ISLRfid/hitag2-emulator/hardware/kicad/HiTag2_Emulator.kicad_sch

## KiCad design hardware/kicad/HiTag2_Emulator.kicad_sch (2025-12-26)

Schematic: HiTag2_Emulator.kicad_sch

Parts:
C1: 22µF; C_0805_2012Metric
C2, C11: 10µF; C_0805_2012Metric
C3, C4, C5, C6, C7, C8: 100nF; R_0603_1608Metric
C9, C10: 18pF; R_0603_1608Metric
C12, C13, C14: 4.7nF; R_0603_1608Metric
J1: SPI_Arduino; PinHeader_1x06_P2.54mm_Vertical
J2: CTRL_Arduino; PinHeader_1x04_P2.54mm_Vertical
J3: ICSP; PinHeader_1x03_P2.54mm_Vertical
J4: ANTENNA; PinHeader_1x02_P2.54mm_Vertical
LED1: Green; LED_0603_1608Metric
LED2: Red; LED_0603_1608Metric
R1: 10kΩ; R_0603_1608Metric
R2, R3: 330Ω; R_0603_1608Metric
R4, R5: 100kΩ; R_0603_1608Metric
R6: 1MΩ; R_0603_1608Metric
R7, R8: 100Ω; R_0603_1608Metric
U1: PIC32MX795F512L-80I/PF; TQFP-100_14x14mm_P0.5mm
U2: AMS1117-3.3; SOT-223-3_TabPin2
U3: LM358; SOIC-8_3.9x4.9mm_P1.27mm
U4: SN74LVC1G17; SOT-23-5
Y1: 8MHz; Crystal_HC49-U_Vertical
